liliumjsn/OrbyTrack/Design/Renders/render_1.jpg

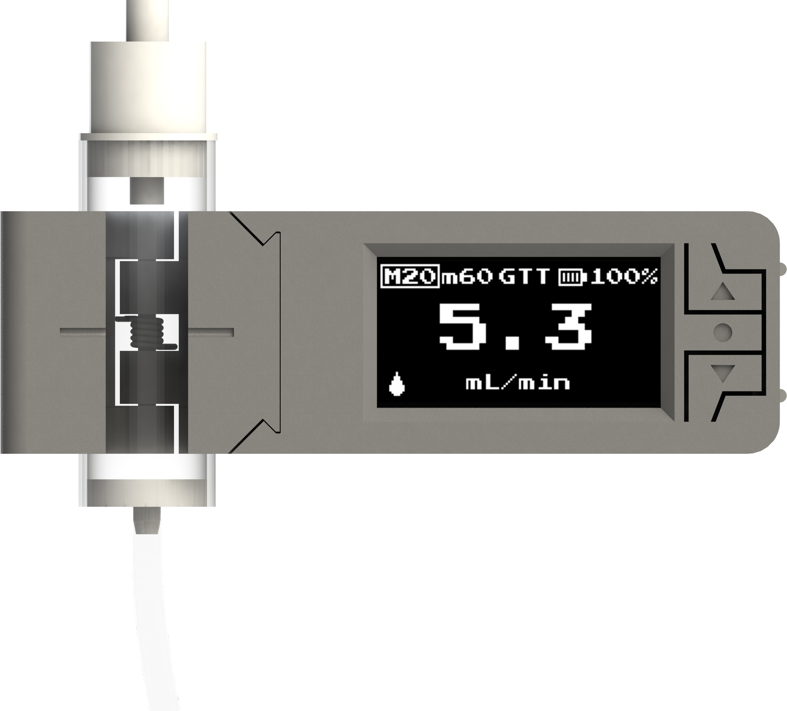
Design/Renders/render_1.jpg
