liliumjsn/OrbyTrack/Firmware/include/ui_bitmaps.h

#ifndef UI_BITMAPS_H
#define UI_BITMAPS_H

const unsigned char epd_bitmap_logo_name [] PROGMEM = {
	0x00, 0xc6, 0x00, 0x00, 0x1e, 0x00, 0x00, 0x01, 0xff, 0xf8, 0x00, 0x00, 0x00, 0x00, 0x1e, 0x00, 
	0x03, 0xc7, 0x80, 0x00, 0x1e, 0x00, 0x00, 0x01, 0xff, 0xf8, 0x00, 0x00, 0x00, 0x00, 0x1e, 0x00, 
	0x0f, 0x83, 0xe0, 0x00, 0x1e, 0x00, 0x00, 0x01, 0xff, 0xf8, 0x00, 0x00, 0x00, 0x00, 0x1e, 0x00, 
	0x1f, 0x83, 0xf0, 0x00, 0x1e, 0x00, 0x00, 0x01, 0xff, 0xf8, 0x00, 0x00, 0x00, 0x00, 0x1e, 0x00, 
	0x1f, 0x83, 0xf0, 0x00, 0x1e, 0x00, 0x00, 0x00, 0x0f, 0x00, 0x00, 0x00, 0x00, 0x00, 0x1e, 0x00, 
	0x3f, 0x01, 0xf8, 0x00, 0x1e, 0x00, 0x00, 0x00, 0x0f, 0x00, 0x00, 0x00, 0x00, 0x00, 0x1e, 0x00, 
	0x7f, 0x01, 0xfc, 0x60, 0xde, 0x3c, 0x78, 0x1c, 0x0f, 0x03, 0x06, 0x0f, 0x80, 0x1f, 0x1e, 0x1e, 
	0x7e, 0x00, 0xfc, 0x73, 0xde, 0x7e, 0x78, 0x1c, 0x0f, 0x03, 0x9e, 0x7f, 0xc0, 0xff, 0x9e, 0x1e, 
	0xfe, 0x00, 0xfe, 0x7b, 0xdf, 0xfe, 0x78, 0x1c, 0x0f, 0x03, 0xde, 0xff, 0xe1, 0xff, 0x9e, 0x3c, 
	0x00, 0x00, 0x00, 0x7f, 0xdf, 0xff, 0x38, 0x3c, 0x0f, 0x03, 0xfe, 0xf1, 0xe1, 0xf3, 0x9e, 0x7c, 
	0x00, 0x00, 0x00, 0x7f, 0x9f, 0x8f, 0x3c, 0x3c, 0x0f, 0x03, 0xfc, 0xc1, 0xe3, 0xe0, 0x1e, 0x78, 
	0xfc, 0x00, 0x7e, 0x7e, 0x1f, 0x0f, 0x3c, 0x3c, 0x0f, 0x03, 0xf0, 0x01, 0xe3, 0xc0, 0x1e, 0x78, 
	0xf8, 0x00, 0x3e, 0x78, 0x1e, 0x0f, 0x1e, 0x38, 0x0f, 0x03, 0xc0, 0x0f, 0xe3, 0xc0, 0x1f, 0xf0, 
	0xf8, 0x00, 0x3e, 0x78, 0x1e, 0x0f, 0x1e, 0x78, 0x0f, 0x03, 0xc0, 0x3f, 0xe3, 0xc0, 0x1f, 0xe0, 
	0xf0, 0x00, 0x1e, 0x78, 0x1e, 0x0f, 0x1e, 0x78, 0x0f, 0x03, 0xc0, 0x7f, 0xe3, 0xc0, 0x1f, 0xf0, 
	0x70, 0x00, 0x1c, 0x78, 0x1e, 0x0f, 0x1e, 0x78, 0x0f, 0x03, 0xc0, 0xf0, 0xe3, 0xc0, 0x1f, 0xf0, 
	0x70, 0x00, 0x1c, 0x78, 0x1e, 0x0f, 0x0e, 0x70, 0x0f, 0x03, 0xc0, 0xf0, 0xe3, 0xc0, 0x1e, 0x78, 
	0x30, 0x00, 0x18, 0x78, 0x1f, 0x1f, 0x0f, 0xf0, 0x0f, 0x03, 0xc0, 0xf1, 0xf3, 0xe0, 0x1e, 0x7c, 
	0x18, 0x00, 0x30, 0x78, 0x1f, 0xbe, 0x0f, 0xf0, 0x0f, 0x03, 0xc0, 0xff, 0xf9, 0xf9, 0x9e, 0x3c, 
	0x18, 0x00, 0x30, 0x78, 0x1f, 0xfe, 0x07, 0xe0, 0x0f, 0x03, 0xc0, 0xff, 0xf9, 0xff, 0x9e, 0x3e, 
	0x0c, 0x00, 0x60, 0x78, 0x1f, 0xfc, 0x07, 0xe0, 0x0f, 0x03, 0xc0, 0x7e, 0xf8, 0x7f, 0x9e, 0x1e, 
	0x06, 0x00, 0xc0, 0x78, 0x03, 0xe0, 0x01, 0xe0, 0x0f, 0x03, 0xc0, 0x38, 0x70, 0x3f, 0x1e, 0x0f, 
	0x00, 0x00, 0x00, 0x00, 0x00, 0x00, 0x01, 0xe0, 0x00, 0x00, 0x00, 0x00, 0x00, 0x00, 0x00, 0x00, 
	0x00, 0x00, 0x00, 0x00, 0x00, 0x00, 0x01, 0xc0, 0x00, 0x00, 0x00, 0x00, 0x00, 0x00, 0x00, 0x00, 
	0x00, 0x00, 0x00, 0x00, 0x00, 0x00, 0x3f, 0xc0, 0x00, 0x00, 0x00, 0x00, 0x00, 0x00, 0x00, 0x00, 
	0x00, 0x00, 0x00, 0x00, 0x00, 0x00, 0x3f, 0xc0, 0x00, 0x00, 0x00, 0x00, 0x00, 0x00, 0x00, 0x00, 
	0x00, 0x00, 0x00, 0x00, 0x00, 0x00, 0x3f, 0x80, 0x00, 0x00, 0x00, 0x00, 0x00, 0x00, 0x00, 0x00, 
	0x00, 0x00, 0x00, 0x00, 0x00, 0x00, 0x3e, 0x00, 0x00, 0x00, 0x00, 0x00, 0x00, 0x00, 0x00, 0x00
}; // 128x28px

const unsigned char epd_bitmap_logo [] PROGMEM = {
	0x00, 0xc6, 0x00, 0x03, 0xc7, 0x80, 0x0f, 0x83, 0xe0, 0x1f, 0x83, 0xf0, 0x1f, 0x83, 0xf0, 0x3f, 
	0x01, 0xf8, 0x7f, 0x01, 0xfc, 0x7e, 0x00, 0xfc, 0xfe, 0x00, 0xfe, 0x00, 0x00, 0x00, 0x00, 0x00, 
	0x00, 0xfc, 0x00, 0x7e, 0xf8, 0x00, 0x3e, 0xf8, 0x00, 0x3e, 0xf0, 0x00, 0x1e, 0x70, 0x00, 0x1c, 
	0x70, 0x00, 0x1c, 0x30, 0x00, 0x18, 0x18, 0x00, 0x30, 0x18, 0x00, 0x30, 0x0c, 0x00, 0x60, 0x06, 
	0x00, 0xc0, 0x00, 0x00, 0x00
}; // 23x23px

const unsigned char epd_bitmap_battery_shell [] PROGMEM = {
	0xff, 0xe0, 0x80, 0x20, 0xa0, 0x30, 0xa0, 0x30, 0xa0, 0x30, 0x80, 0x20, 0xff, 0xe0
}; // 12x7px

const unsigned char epd_bitmap_battery_charging [] PROGMEM = {
	0x00, 0x80, 0x01, 0x00, 0xf3, 0x60, 0x86, 0x20, 0x8c, 0x30, 0x9f, 0xb0, 0x83, 0x30, 0x86, 0x20, 
	0xec, 0xe0, 0x08, 0x00, 0x10, 0x00
}; // 12x11px

const unsigned char epd_bitmap_droplet [] PROGMEM = {
	0x10, 0x10, 0x38, 0x38, 0x7c, 0x7c, 0xfe, 0xfe, 0xfe, 0x7c, 0x38
}; // 7x11px

#endif
